Caleb-Leonard/Power-Systems-Project-Lab-/BuckConvModel.asc

C1: cap; 500n; Rser=1.2
C2: cap; 100µ; Rser=0.7
C3: cap; 500n
C8: cap; 100µ; Rser=1.2
C9: cap; 100µ
D1: schottky; B520C
L1: ind; 100µ; Rser=0.079
L2: ind; 100µ
L3: ind; 100µ
M1: nmos; BSC010NE2LS
NTC: res; 3
R2: res; 12k
R3: res; 6k
R4: res; 12k
R5: res; 6k
R6: res; 12k
R7: res; 6k
R8: res; 12k
R9: res; 6k
R_Load: res; 10
U1: LT1112
U2: LT1112
V1: voltage; 15
V2: voltage; PULSE(0 24 0 0 0 3.5u 10u 100k)
V3: voltage; 10
V4: voltage; 2.048
V5: voltage; 3.3
Named nets: 0, V_Out, 3.3V, V_In, 10V_Ref, 2.048V, V_IN_Meas, V_OUT_Meas
.tran 0 1 0 10u uic
45kHz Filter
3.2kHz Filter
Input Voltage to uController
Output Voltage to uController
